TomDDG/ZXPicoJoy/images/IMG_4924.JPEG

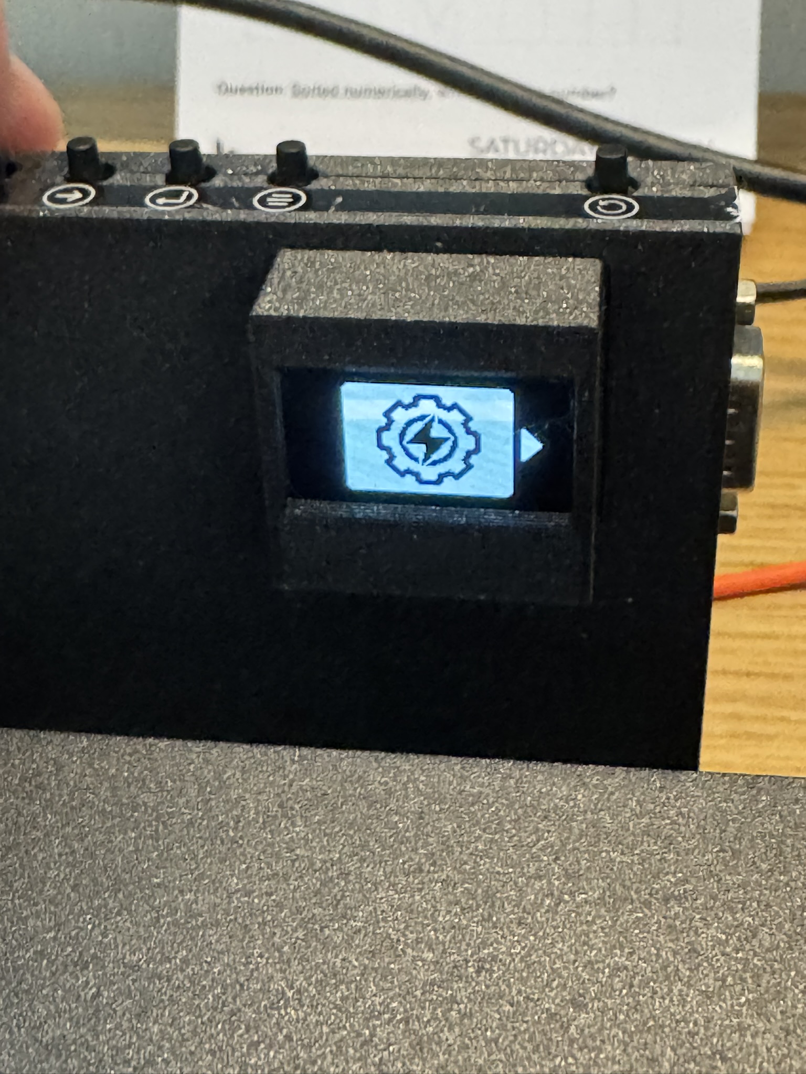
images/IMG_4924.JPEG
