TomDDG/ZXPicoJoy/images/IMG_4925.JPEG

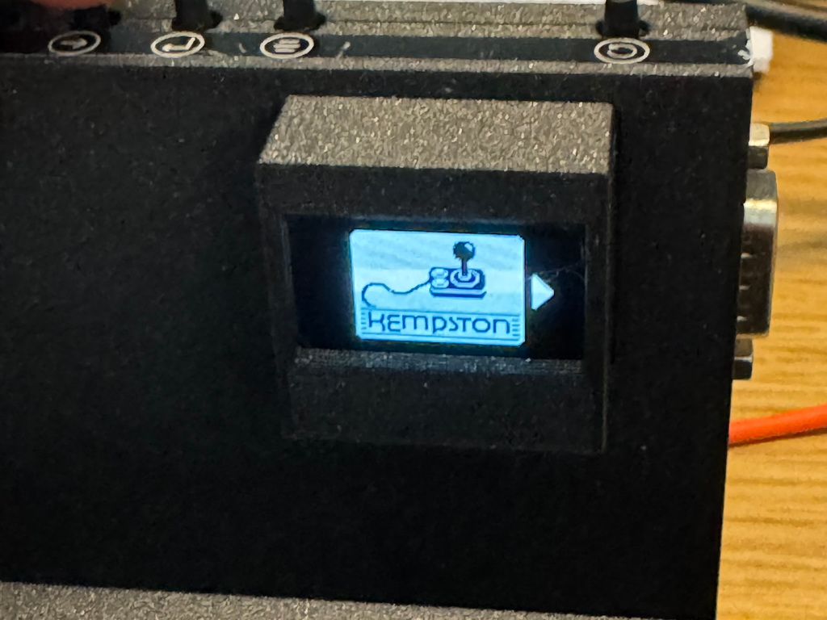
images/IMG_4925.JPEG
