TomDDG/ZXPicoJoy/images/IMG_4926.JPEG

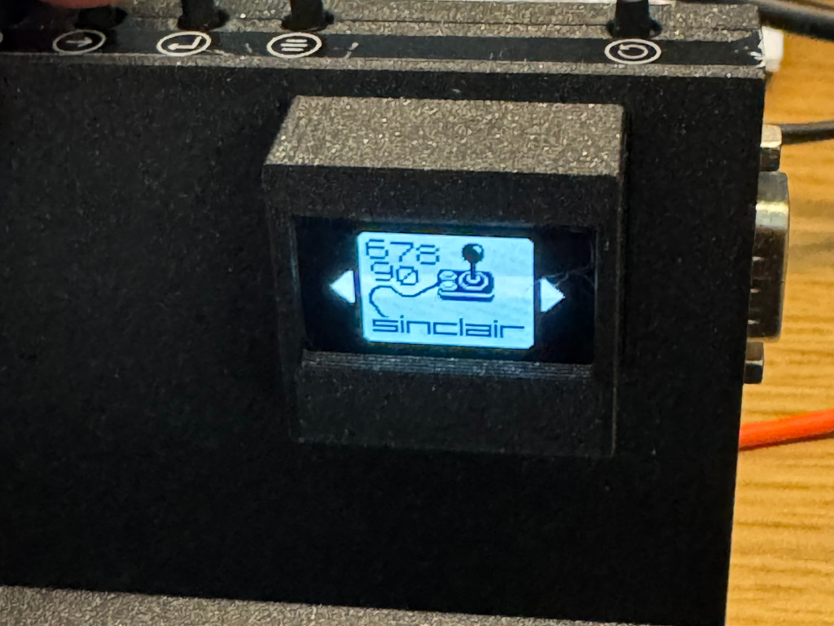
images/IMG_4926.JPEG
