TomDDG/ZXPicoJoy/icons.h

// unpacked icon is 96bytes
// 32*24 or 4x3
// 44 icons = 4224bytes -> 3041bytes saving 1183bytes (28%)
//
    const uint8_t icon_b3[]={ 0x06,0xff,0x03,0x01,0x01,0xe1,0xe1,0x61,0x84,0x00,0x05,0xe1,0xc1,0x81,0x01,0x81,
                              0xc1,0x85,0x0d,0x82,0x0c,0x08,0x03,0xff,0xff,0x00,0x00,0x00,0xff,0xff,0x8c,0x84,
                              0x00,0x09,0xde,0xff,0x73,0x00,0x61,0xe1,0xc0,0x80,0x80,0x80,0x85,0x0c,0x81,0x1a,
                              0x03,0xf0,0xe0,0xe0,0xe1,0x87,0x00,0x00,0xe0,0x82,0x00,0x89,0x0b,0x01,0xf0,0xff,
                              0x80 };
 // 65bytes
    const uint8_t icon_b2[]={ 0x06,0xff,0x03,0x01,0x01,0xe1,0xe1,0x61,0x84,0x00,0x05,0xe1,0xc1,0x81,0x01,0x81,
                              0xc1,0x85,0x0d,0x82,0x0c,0x08,0x03,0xff,0xff,0x00,0x00,0x00,0xff,0xff,0x8c,0x84,
                              0x00,0x06,0xde,0xff,0x73,0x00,0xf1,0xf9,0x9c,0x84,0x0d,0x02,0x8e,0x87,0x83,0x82,
                              0x1a,0x03,0xf0,0xe0,0xe0,0xe1,0x87,0x00,0x00,0xe0,0x8a,0x0c,0x81,0x0e,0x01,0xf0,
                              0xff,0x80 };
 // 66bytes
    const uint8_t icon_b1[]={ 0x06,0xff,0x03,0x01,0x01,0xe1,0xe1,0x61,0x84,0x00,0x0b,0xe1,0xc1,0x81,0x01,0x01,
                              0x81,0xc1,0xe1,0x61,0xe1,0xe1,0x01,0x83,0x00,0x08,0x03,0xff,0xff,0x00,0x00,0x00,
                              0xff,0xff,0x8c,0x84,0x00,0x0b,0xde,0xff,0x73,0x00,0x00,0x81,0x81,0x80,0x80,0xff,
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
                              0x10,0x13,0x82,0x0e,0x00,0x13,0x81,0x1a,0x07,0xff,0xff,0xf0,0xe0,0xe0,0xe1,0xe1,
                              0xe1,0x81,0x04,0x00,0xe0,0x81,0x00,0x84,0x07,0x82,0x0f,0x81,0x13,0x81,0x14,0x01,
                              0xf0,0xff,0x80 };
 // 83bytes
 //
