TomDDG/ZXPicoJoy/scr_img.h

// unpacked screen is 1024bytes
// first 18 screens 73% smaller due to compression
//
// 0 - scr_00 (spash screen) 391bytes
// 1 - scr_01 (1 button joystick) 278bytes
// 2 - scr_02 (bluetooth) 258bytes
// 3 - scr_0101 (kempston) 349bytes
// 4 - scr_0102 (sinclair1) 426bytes
// 5 - scr_0103 (sinclair2) 426bytes
// 6 - scr_0104 (cursor) 460bytes
// 7 - scr_0105 (redefine keys) 507bytes
// 8 - scr_010001a (activate 1 not activated) 332bytes
// 9 - scr_010001b (activate 2 activated) 322bytes
// 10 - scr_010002 (define button 2) 191bytes
// 11 - scr_010003 (define button 3) 159bytes
// 12 - scr_010501 (define up button) 153bytes
// 13 - scr_010502 (define down button) 140bytes
// 14 - scr_010503 (define left button) 145bytes
// 15 - scr_010504 (define right button) 145bytes
// 16 - scr_010505 (define button 1) 175bytes
// 17 - scr_0201 (ps4 controller) 303bytes
// 18 - scr_0202 (xbox controller) 303bytes
// 19 - scr_010001c (activate standalone) 290bytes
// 20 - setup (flash set-up) 340bytes
// 21 - scr_reset (reset flash) 370bytes
// 22 - setup 90 (animation for 19) 344bytes
//
    const uint8_t scr_00[]={ 0x08,0x00,0xc0,0xf0,0xf8,0xfc,0xfc,0xfe,0xfe,0xff,0x8e,0x00,0x05,0xef,0xef,0x6f,
                                0xaf,0xcf,0xef,0x81,0x07,0x03,0xdf,0x3f,0x3f,0xdf,0x81,0x07,0x86,0x20,0x01,0x0f,
                                0x6f,0x81,0x00,0x00,0x9f,0x81,0x2e,0x01,0xbf,0x2f,0x84,0x33,0x03,0x3f,0xdf,0xdf,
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
                                  0x0f,0x81,0x0c,0x00,0x83,0x82,0x15,0x81,0x1c,0x01,0x81,0xc0,0x82,0x88,0x00,0xfe,
                                  0x93,0x42,0xa6,0xff,0x00,0x3f,0x85,0x58,0x9a,0x05,0x81,0x8d,0x89,0x00,0x84,0xfa,
                                  0x9c,0x35,0x01,0x7f,0x3f,0x92,0xff,0x80 };
 // 344bytes
